oliviahanley/wren-keyboard/images/variations.jpeg

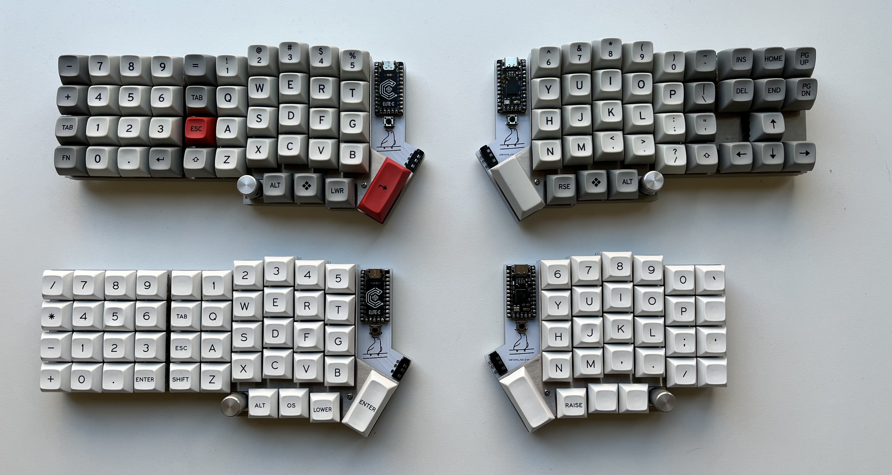
images/variations.jpeg
