oliviahanley/wren-keyboard/images/wren-all.png

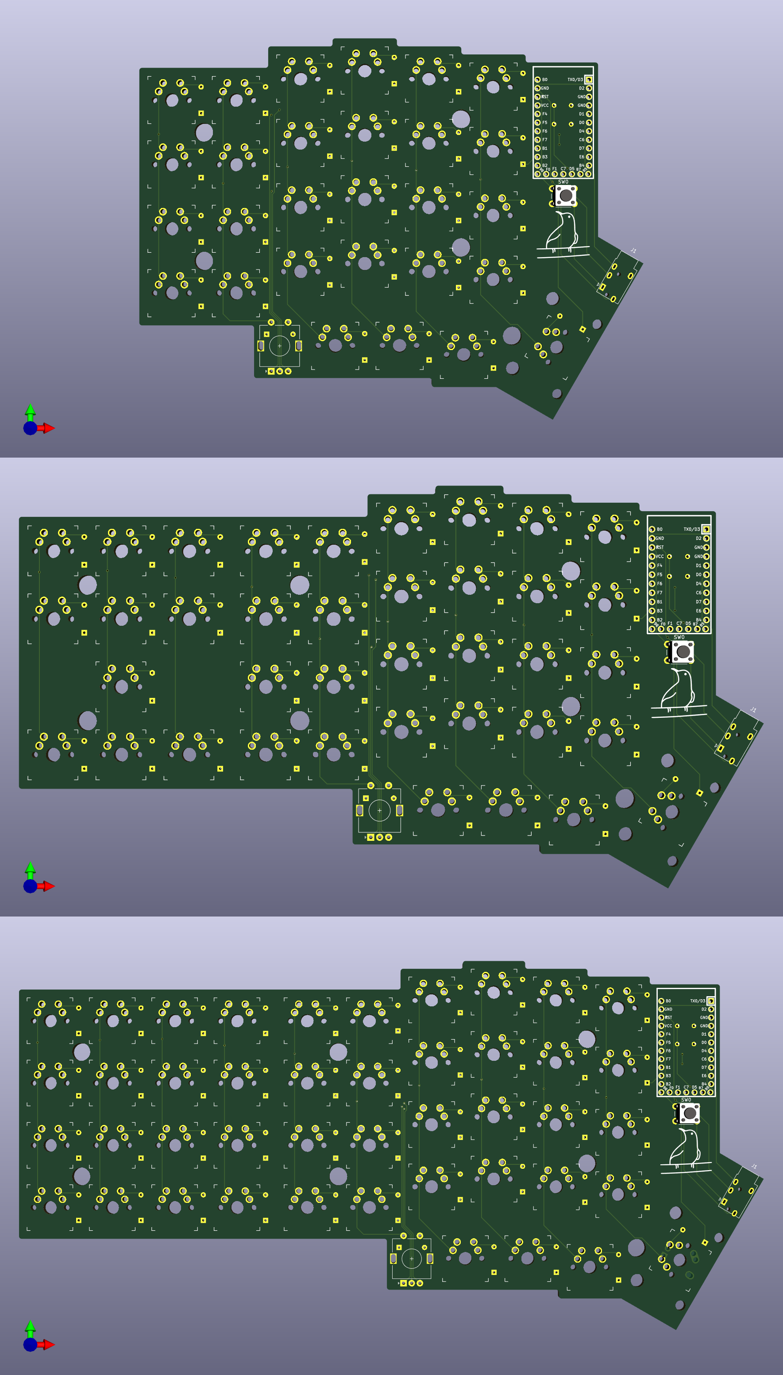
images/wren-all.png
