oliviahanley/wren-keyboard/images/wren-nav.png

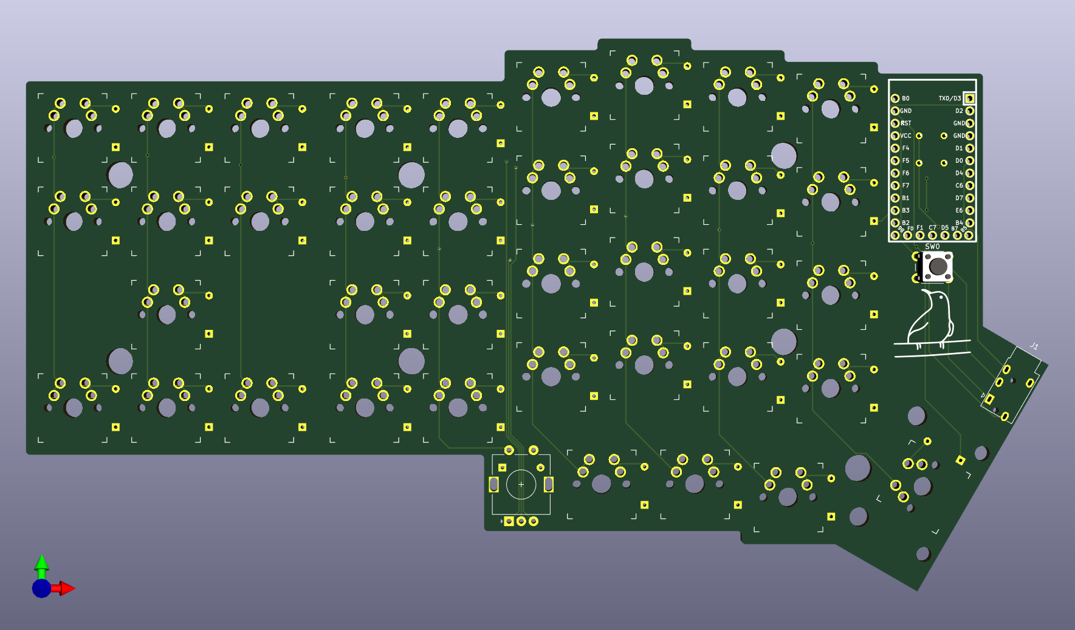
images/wren-nav.png
