oliviahanley/wren-keyboard/images/wren-numpad.png

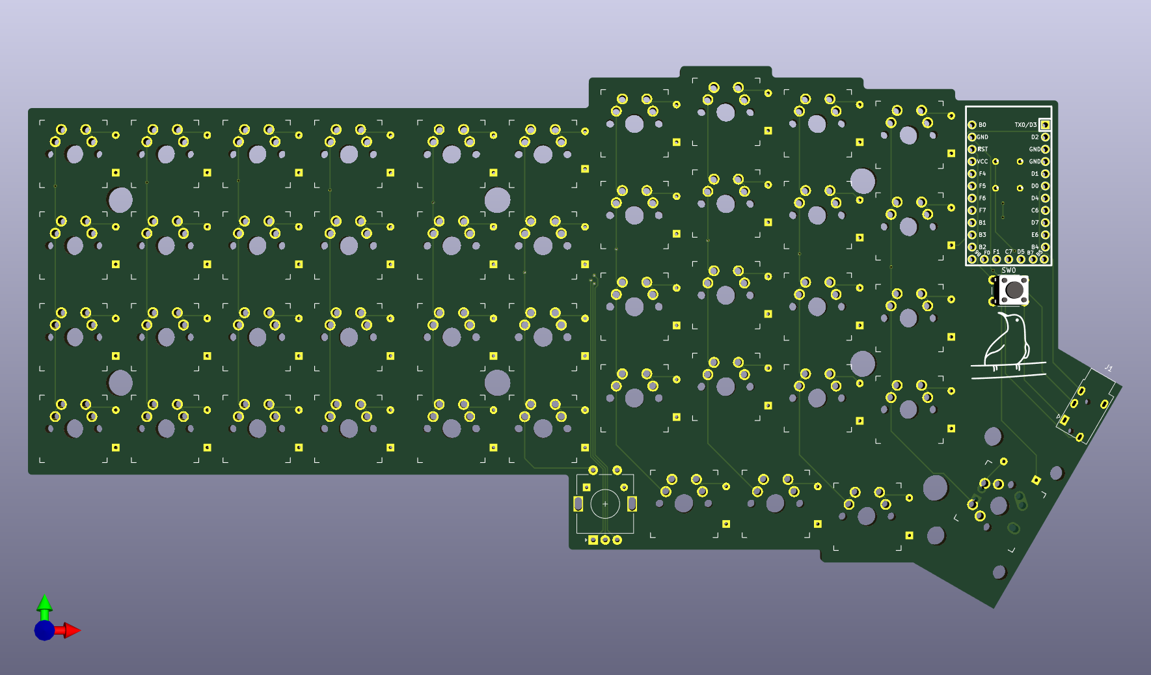
images/wren-numpad.png
