oliviahanley/wren-keyboard/images/wren-plain.png

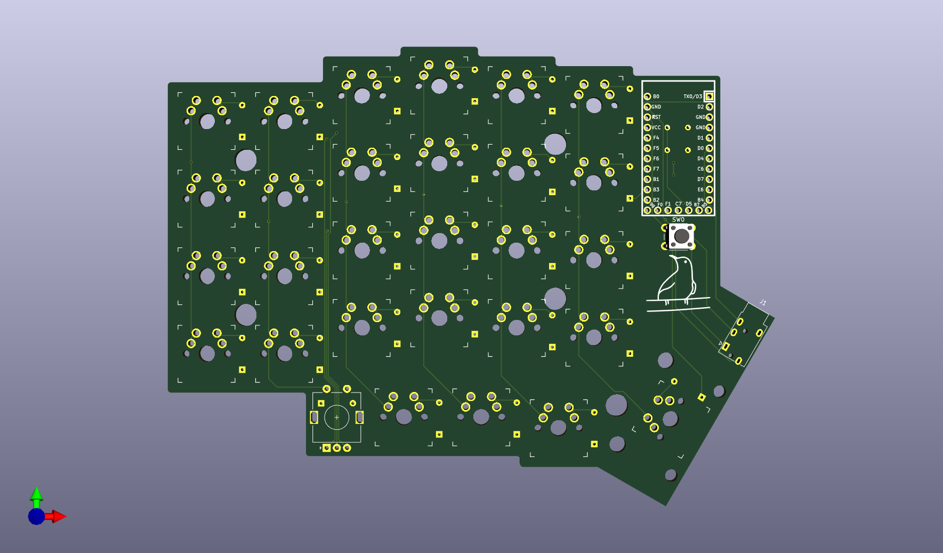
images/wren-plain.png
