oliviahanley/wren-keyboard/images/tutorial/26_switchplate_finished.jpeg

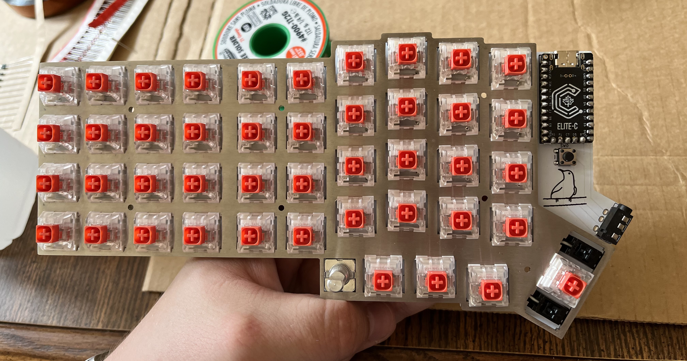
images/tutorial/26_switchplate_finished.jpeg
